daviderovell0/bzzzbz/media/audio_breakout.jpg

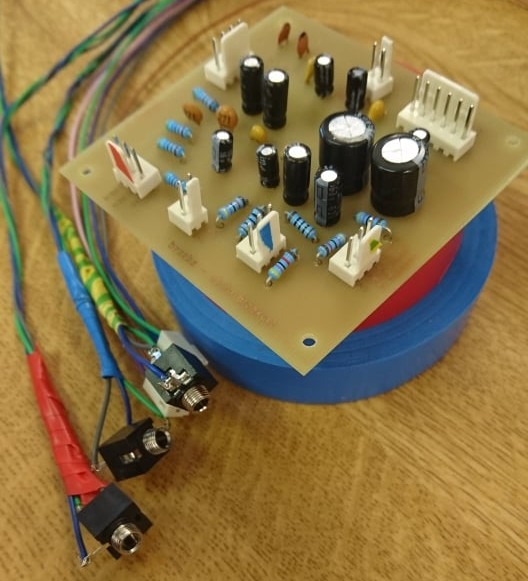
media/audio_breakout.jpg
