daviderovell0/bzzzbz/media/board_v2_3D_bottom.png

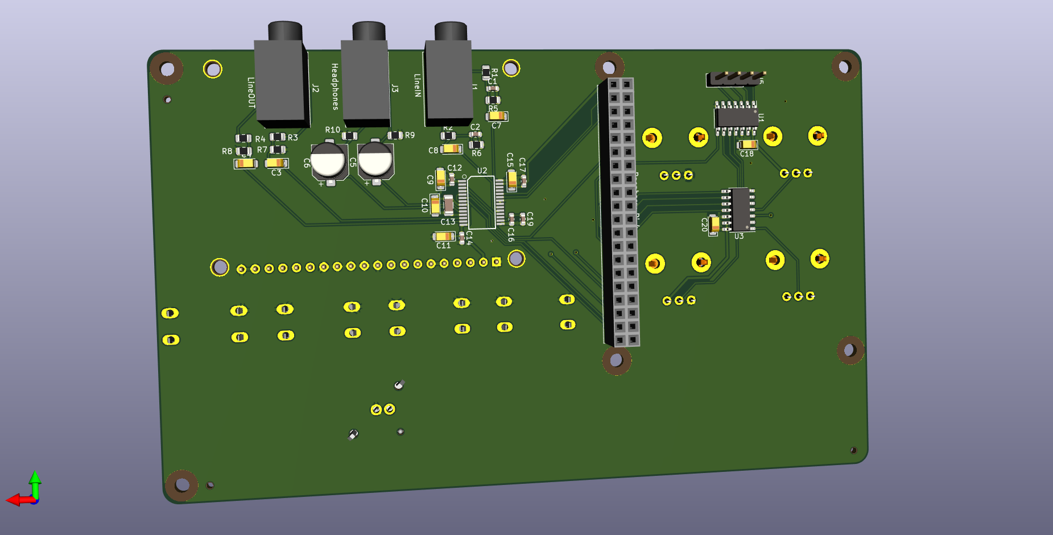
media/board_v2_3D_bottom.png
