daviderovell0/bzzzbz/media/board_v2_3D_front.png

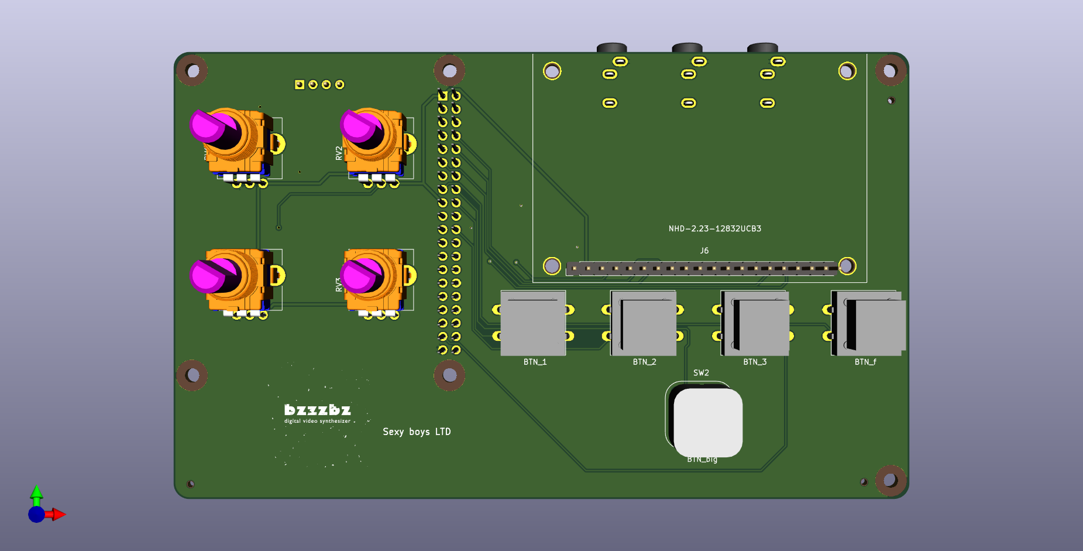
media/board_v2_3D_front.png
