daviderovell0/bzzzbz/media/board_v2_3D_side.png

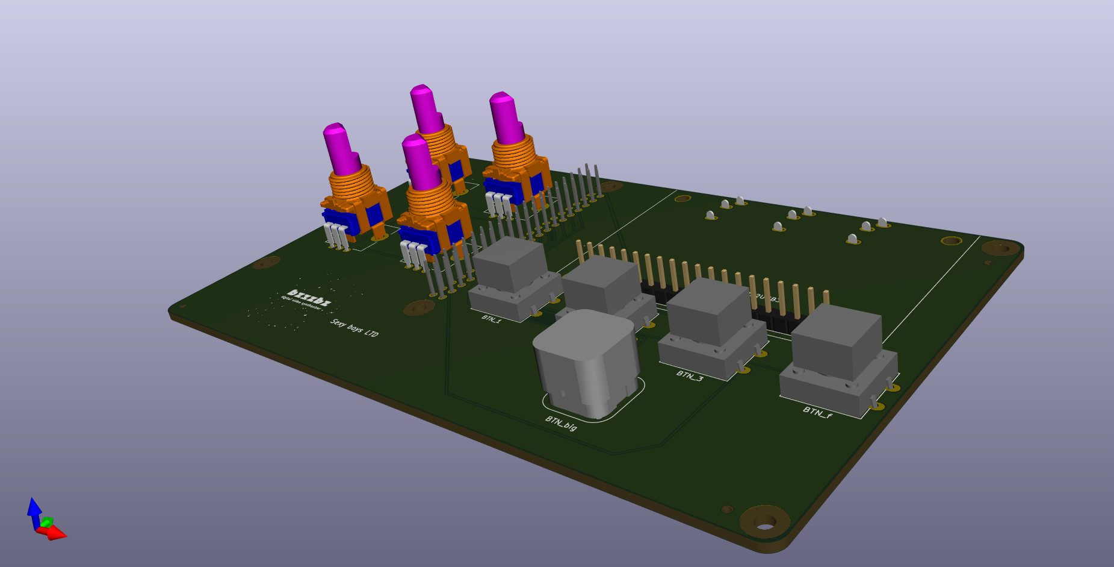
media/board_v2_3D_side.png
