daviderovell0/bzzzbz/media/control_breakout.jpg

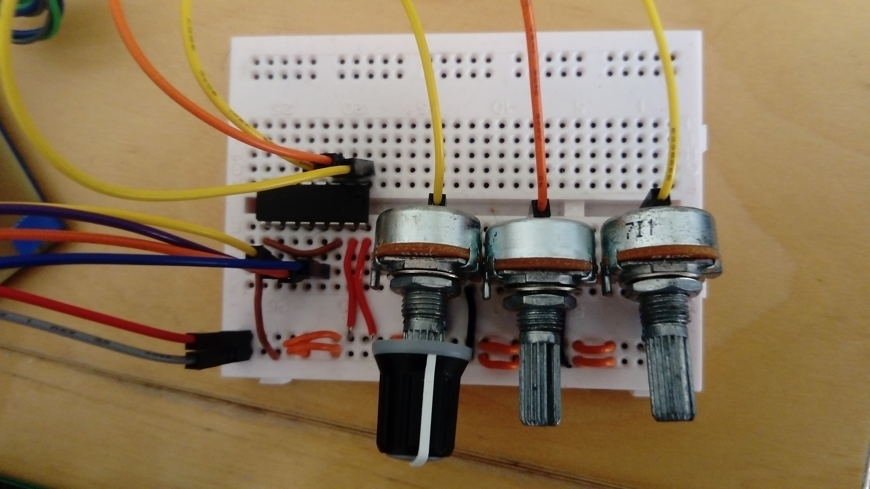
media/control_breakout.jpg
