daviderovell0/bzzzbz/media/frequencytestofbzzzbz.jpg

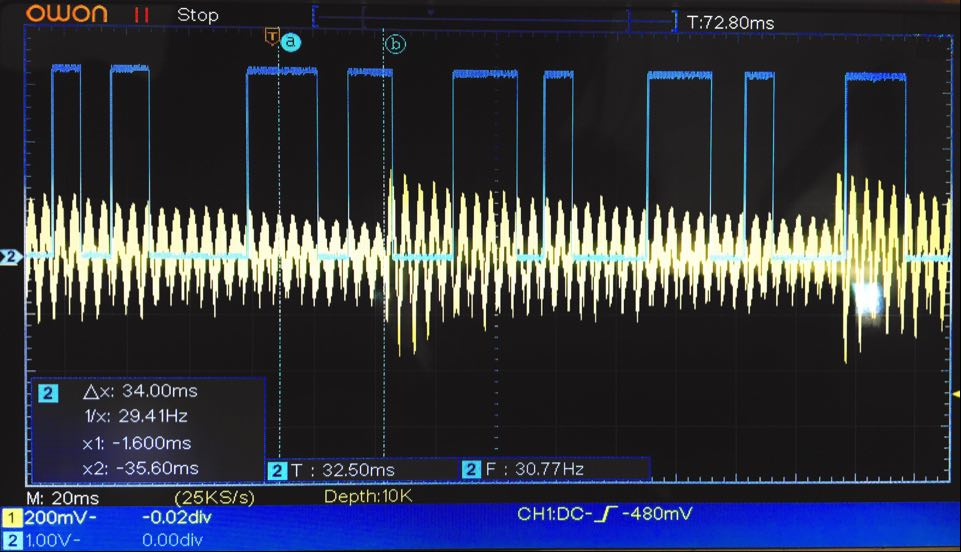
media/frequencytestofbzzzbz.jpg
