daviderovell0/bzzzbz/media/latencytestbzzzbz.jpg

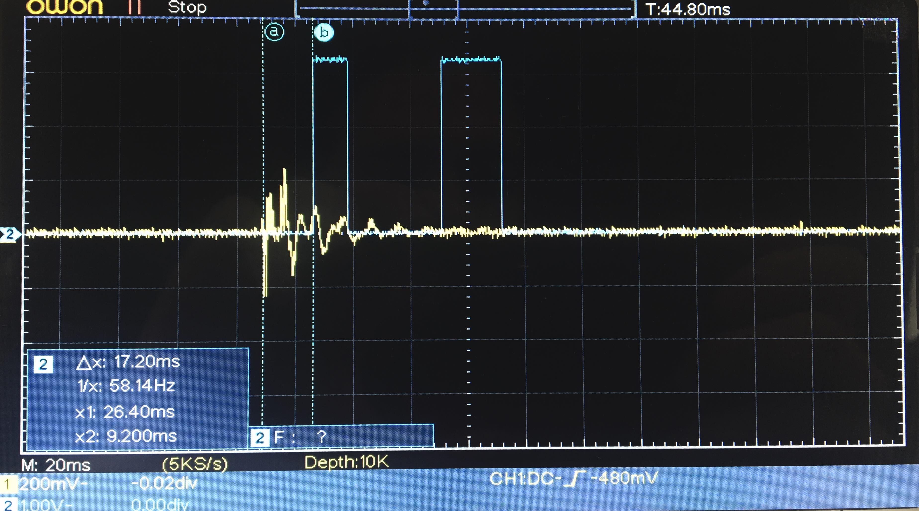
media/latencytestbzzzbz.jpg
