daviderovell0/bzzzbz/media/software_diagram1.png

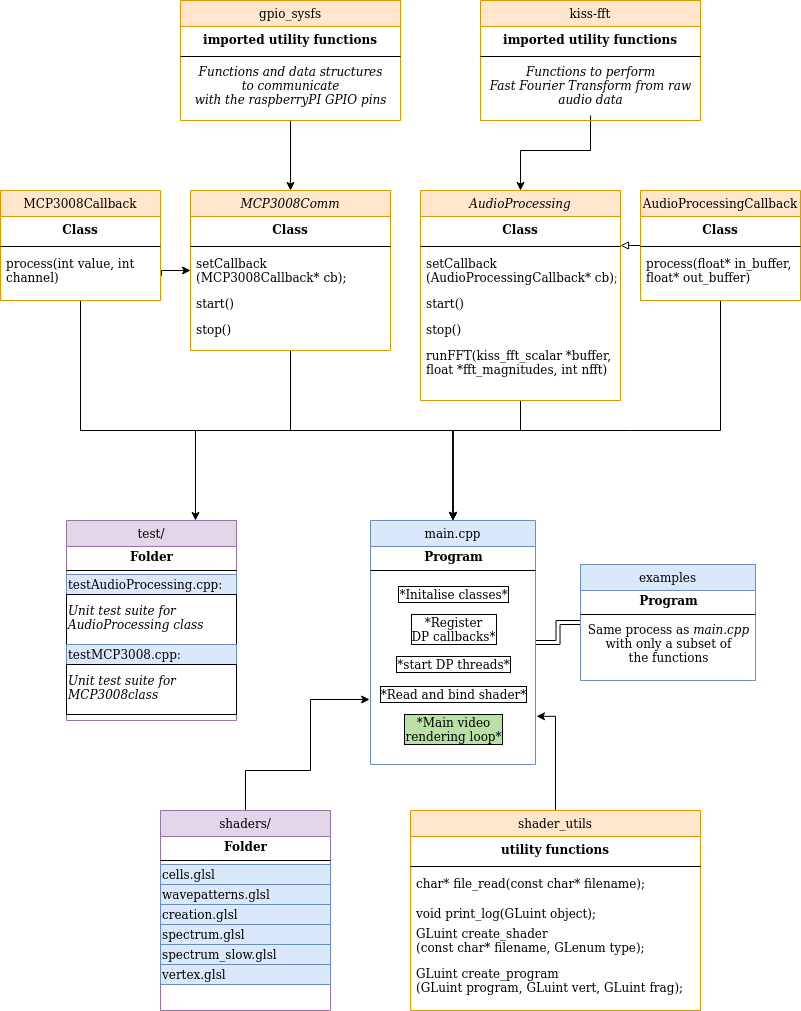
media/software_diagram1.png
