daviderovell0/bzzzbz/src/MCP3004Comm.h

/** @file MCP3004Comm.h
 * 
 * @brief Class for acquiring data from the MCP3004 ADC. (board v2)
 *
 * @author Marcell Illyes (marcellillyes), Davide Rovelli (daviderovell0)
 * 
 */

#ifndef __MCP3004COMM_H
#define __MCP3004COMM_H

#include <stdint.h>
#include <unistd.h>
#include <stdio.h>
#include <stdlib.h>
#include <fcntl.h>
#include <sys/ioctl.h>
#include <linux/types.h>
#include <linux/spi/spidev.h>
#include <thread>  

#include "gpio-sysfs.h"

/**
 * \class MCP3004callback
 * 
 * \brief Callback attached to the MCP3004Comm class running in a separate 
 * data acquisition thread.
 **/
class MCP3004callback {
public:
	/**
	 * \brief Called after a sample has arrived.
	 * 
	 * \param int value - value from the ADC
	 * \param int channel - ADC input channel associated with the value
	 **/
	virtual void hasSample(int value, int channel) = 0;
};


/**
 * \class MCP3004Comm
 * \brief This class reads data from the MCP3004 in the background (separate
 * thread) and calls a callback function whenever data is available.
 **/
class MCP3004Comm {

public:
	/**
	 * \brief Constructor with the spiDevice. The default device
	 * is /dev/spidev0.0.
	 * 
	 * \param const char* spiDevice - the SPI interface of the Raspberry Pi.
	 **/
	MCP3004Comm(const char* spiDevice = "/dev/spidev0.0");

	/**
	 * \brief Sets the callback which is called whenever there is a sample
	 * 
	 * \param MCP3004callback* cb - Pointer to the callback instance.
	 **/
	void setCallback(MCP3004callback* cb);

	/**
	 * \brief Starts the data acquisition in the background and the
	 * callback is called with new samples
	 * 
	 **/
	void start();

	/**
	 * \brief Stops the data acquistion and frees data structures
	 **/
	void stop();




private:
	const uint8_t SINGLE_CHANNEL [8] = {0x80, 0x90, 0xA0, 0xB0};
	const uint8_t DIFF_CHANNEL [8] = {0x00, 0x10, 0x20, 0x30};
	const uint16_t MASK = 1023; /* 10bit mask to filter useful data */
	const uint8_t CS = 8;
	const uint8_t mode = SPI_CPHA | SPI_CPOL;
	const uint32_t speed = 500000;
	const uint16_t delay = 0;
	const uint8_t bpw   = 8;
	
	int fd = 0;
	std::thread* daqThread = NULL;
	int running = 0;
	MCP3004callback* mcp3004callback = NULL;

	int spi_transfer(int fd, uint8_t* tx, uint8_t* rx, int n);
	int readData(int fd, uint8_t ch);
	static void run(MCP3004Comm* mcp3004comm);

};


#endif
